hanachi-ap/willow64-doc/img/bottom-cover-left.jpg

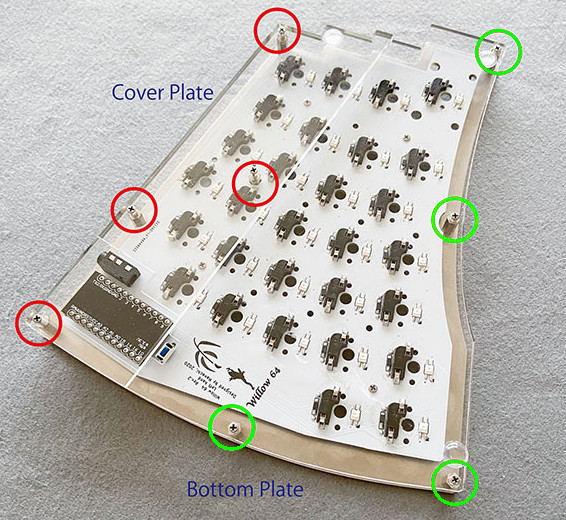
img/bottom-cover-left.jpg
