hanachi-ap/willow64-doc/img/img12.jpg

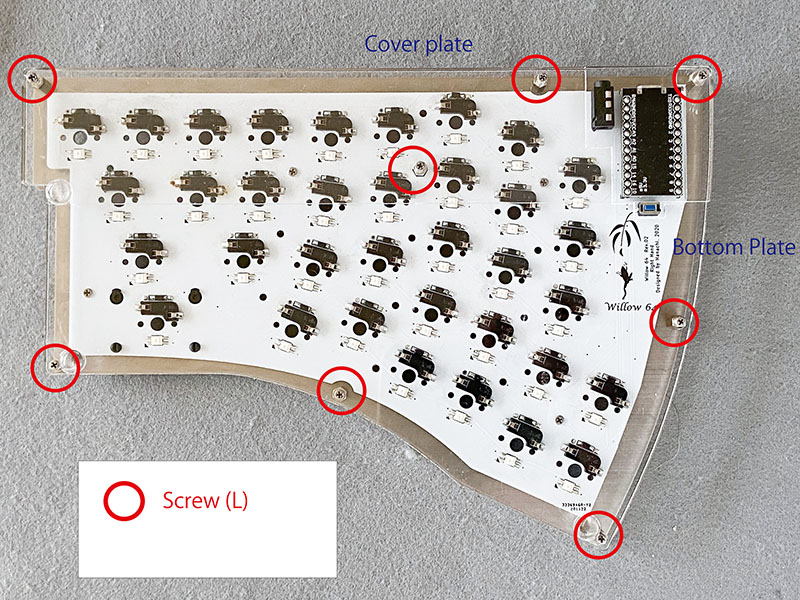
img/img12.jpg
