hanachi-ap/willow64-doc/img/img13.jpg

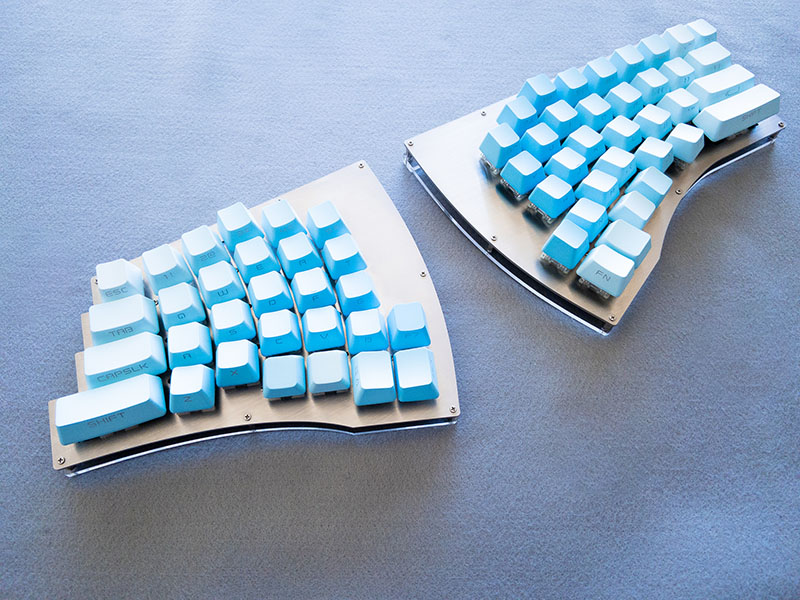
img/img13.jpg
