hanachi-ap/willow64-doc/img/img15.JPG

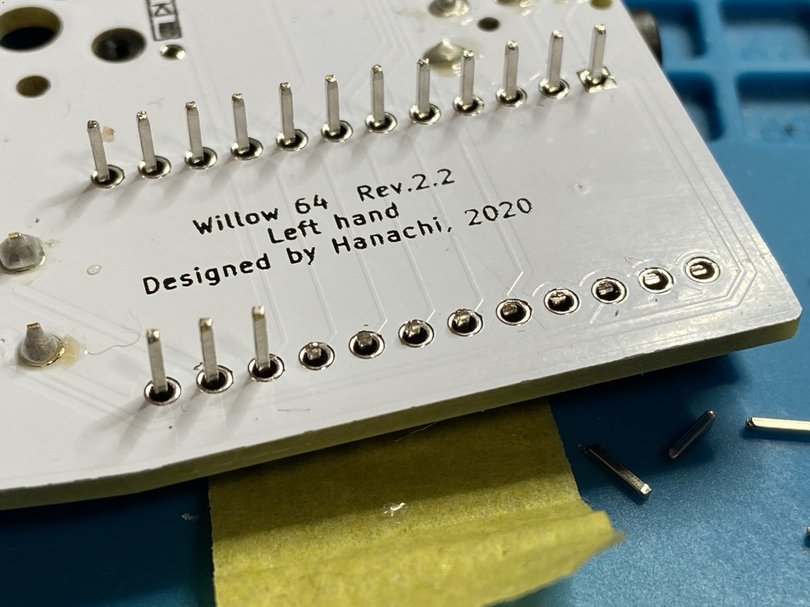
img/img15.JPG
