hanachi-ap/willow64-doc/img/img16.JPG

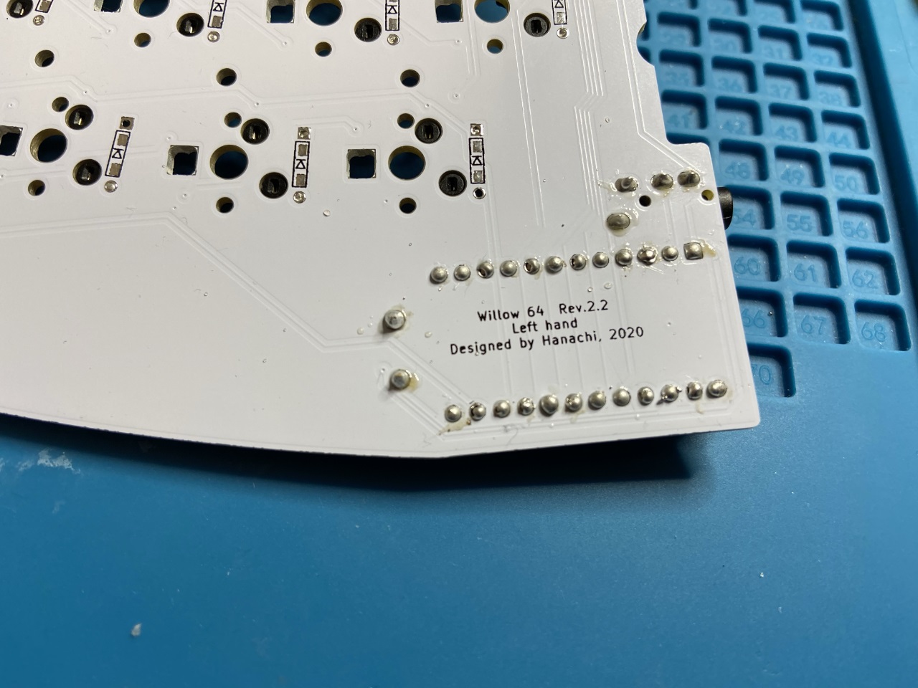
img/img16.JPG
