hanachi-ap/willow64-doc/img/sub-legs.jpg

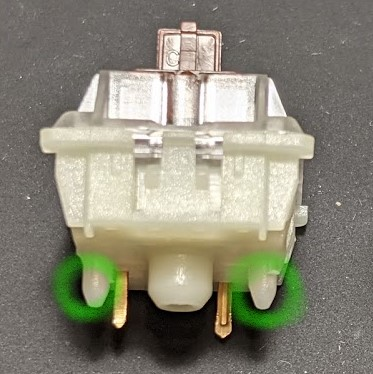
img/sub-legs.jpg
