hanachi-ap/willow64-doc/img/switch-adjustment-left.jpg

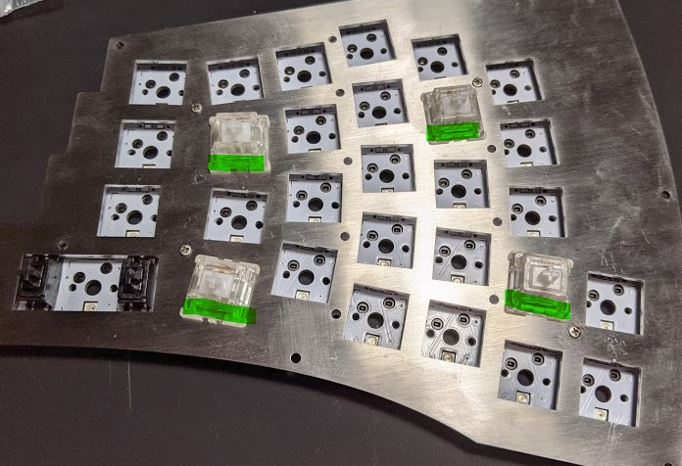
img/switch-adjustment-left.jpg
