hanachi-ap/willow64-doc/img/switch-incomplete-insertion.jpg

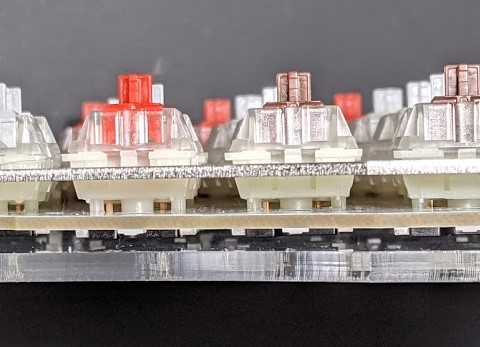
img/switch-incomplete-insertion.jpg
