hanachi-ap/willow64-doc/img/switch-insertion.jpg

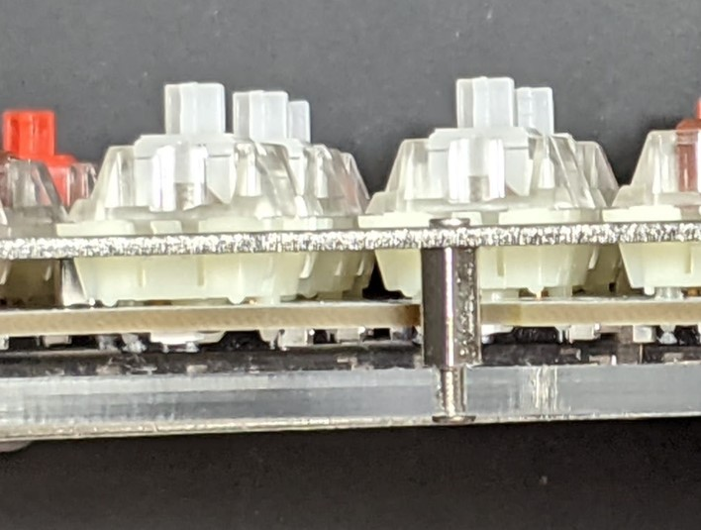
img/switch-insertion.jpg
